rachelparkinson/beehaviour-lab/control/LED_panels.py

import RPi.GPIO as GPIO
import time

def lights(R_LED_PIN, W_LED_PIN, LED_time):
    #use standard GPIO numbers:
    #GPIO.setmode(GPIO.BCM) #is this necessary anywhere??

    #set as output pin (GPIO.IN = input pin)
    GPIO.setup(R_LED_PIN, GPIO.OUT)
    GPIO.setup(W_LED_PIN, GPIO.OUT)
    
    while True:
        #Turn on white LED panel
        GPIO.output(W_LED_PIN, GPIO.HIGH)

        #wait "LED_time" duration
        time.sleep(LED_time)

        #Turn off white LED panel, turn on red LEDs
        GPIO.output(W_LED_PIN, GPIO.LOW)
        GPIO.output(R_LED_PIN, GPIO.HIGH)

        #Wait LED_time duration
        time.sleep(LED_time)

        #turn off red LEDs
        GPIO.output(R_LED_PIN, GPIO.LOW)
